NVSL/QuadClass-Remote/images/IMG_7027.jpg

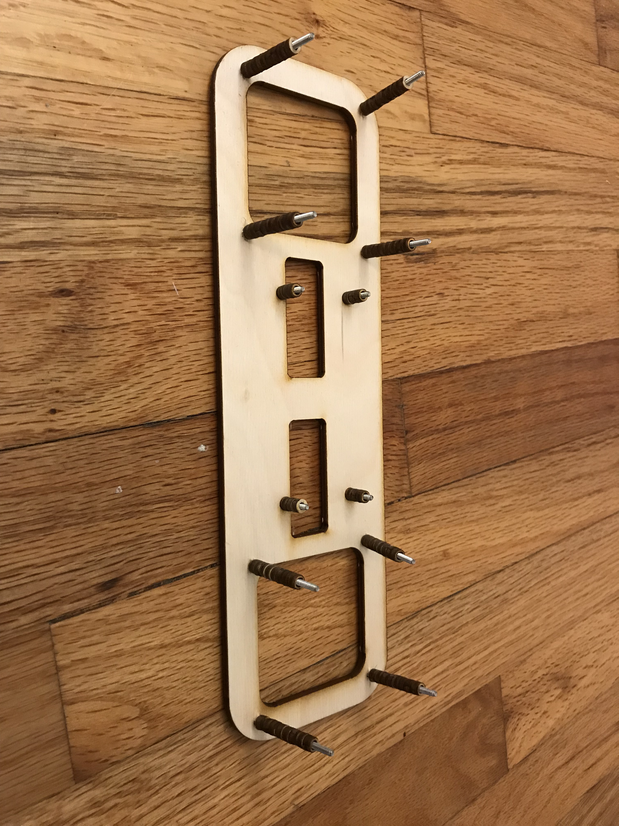
images/IMG_7027.jpg
