NVSL/QuadClass-Remote/images/IMG_7028.jpg

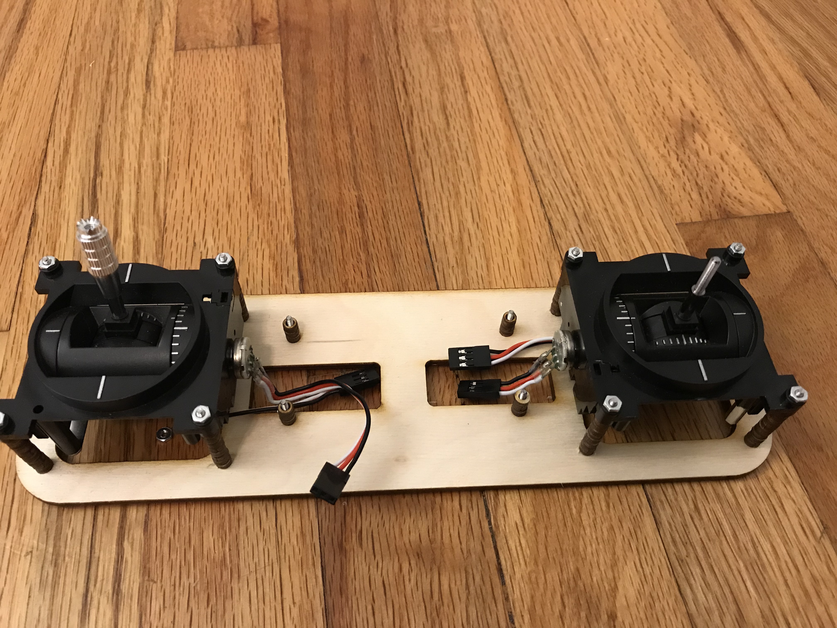
images/IMG_7028.jpg
