NVSL/QuadClass-Remote/images/IMG_7030.jpg

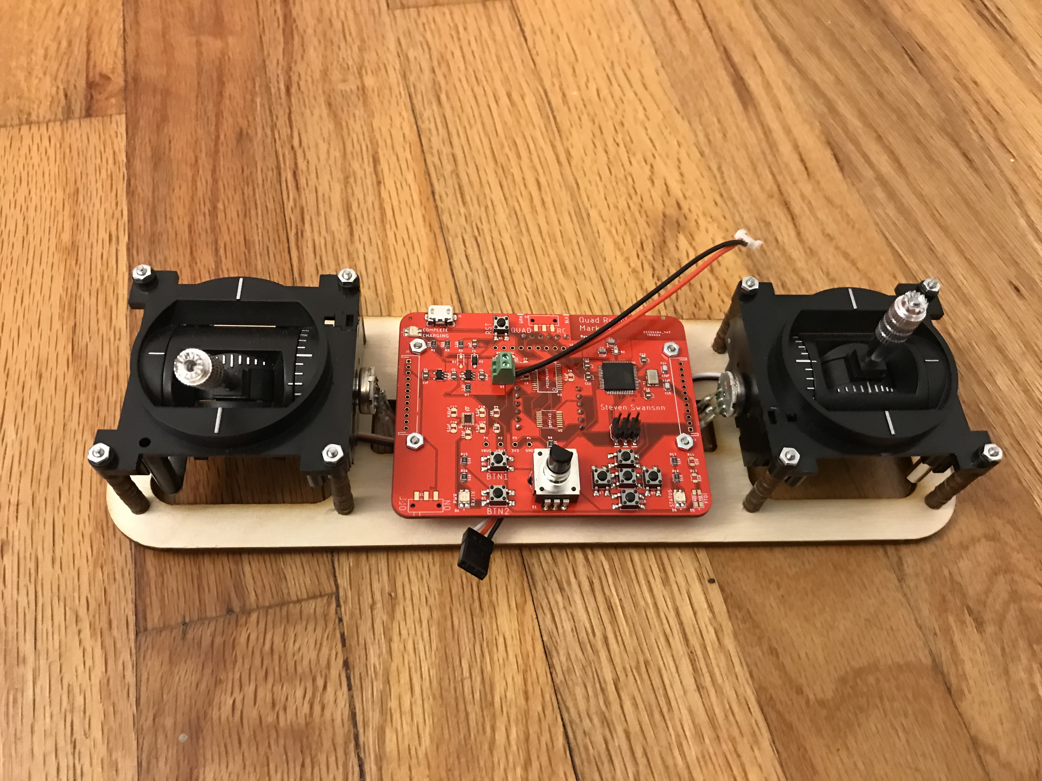
images/IMG_7030.jpg
