NVSL/QuadClass-Remote/images/IMG_7031.jpg

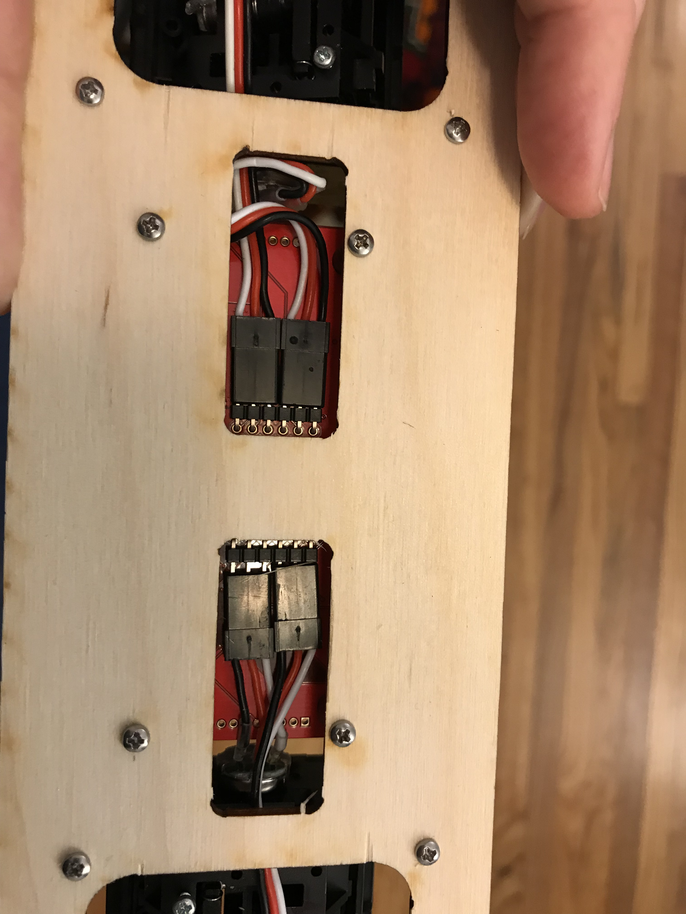
images/IMG_7031.jpg
