NVSL/QuadClass-Remote/images/IMG_7032.jpg

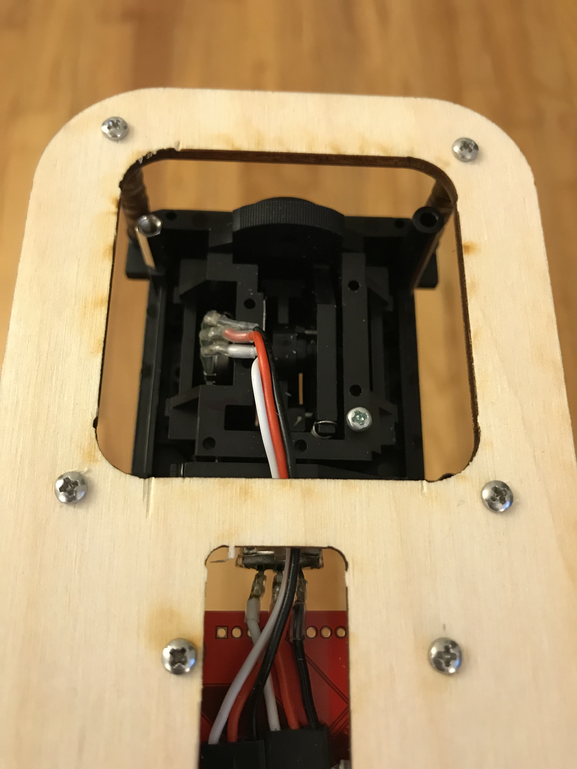
images/IMG_7032.jpg
