NVSL/QuadClass-Remote/multicharger/multicharger.brd

## EAGLE design multicharger/multicharger.brd (2020-02-13)

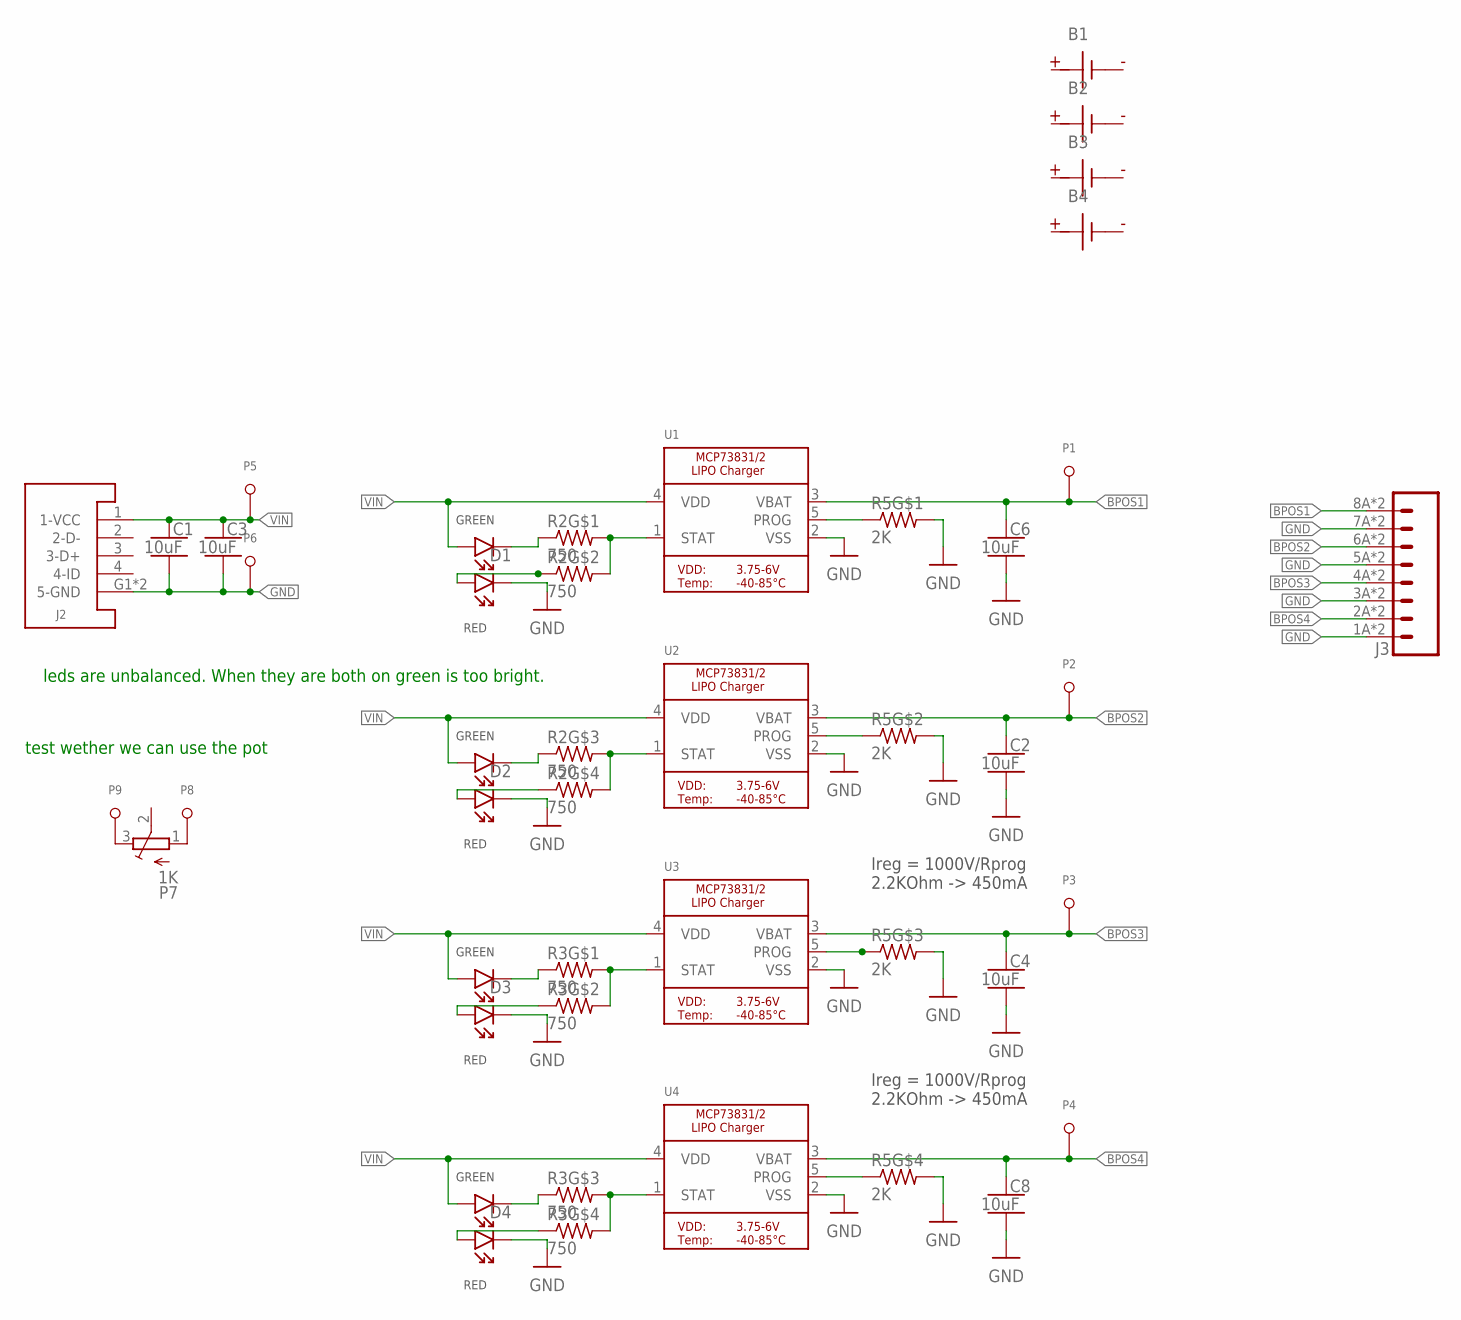
[picture p17: schematic multicharger.sch]

Parts:
B1, B2, B3, B4: BATTERY-SMD; MOLEX-BATTERY-CONNECTOR-SMD-51005-2P
C1, C2, C3, C4, C6, C8: 10uF; CAPC1608X100
D1, D2, D3, D4: LED-2X-GREEN/RED-1.6X1.5MM; LED-2X-LITE-ON-1.6MMX1.5MM
J2: USB-A-SMD-KEYSTONE-931; USB-A-KEYSTONE-931
J3: HEADER-8POS-; WIRE-TERMINAL-1X8-2.5MM-SMD
P1, P2, P3, P4, P5, P6, P8, P9: TEST-POINT-1MM; TEST-POINT-1MM-VIA
P7: 1K; BOT-ADJUST-POT-3314R-1-103E
R2, R3: 750; RESCAXS50P200X100X45-8
R5: 2K; RESCAXS50P200X100X45-8
U1, U2, U3, U4: MCP73831T-2ACI/OT; SOT23-5

Connections:
BPOS1: C6.1, J3.8A (8), J3.8B (8), P1.T, U1.3 (VBAT)
BPOS2: C2.1, J3.6A (6), J3.6B (6), P2.T, U2.3 (VBAT)
BPOS3: C4.1, J3.4A (4), J3.4B (4), P3.T, U3.3 (VBAT)
BPOS4: C8.1, J3.2A (2), J3.2B (2), P4.T, U4.3 (VBAT)
GND: C1.2, C2.2, C3.2, C4.2, C6.2, C8.2, D1.C1, D2.C1, D3.C1, D4.C1, J2.G1 (5-GND), J2.G2 (5-GND), J3.1A (1), J3.1B (1), J3.3A (3), J3.3B (3), J3.5A (5), J3.5B (5), J3.7A (7), J3.7B (7), P6.T, R5.5 (2), R5.6 (2), R5.7 (2), R5.8 (2), U1.2 (VSS), U2.2 (VSS), U3.2 (VSS), U4.2 (VSS)
unnamed: D1.A1, R2.3 (1)
unnamed: D1.C2, R2.4 (1)
unnamed: R2.7 (2), R2.8 (2), U2.1 (STAT)
unnamed: R5.3 (1), U2.5 (PROG)
unnamed: D2.A1, R2.1
unnamed: D2.C2, R2.2 (1)
unnamed: R3.5 (2), R3.6 (2), U3.1 (STAT)
unnamed: R5.2 (1), U3.5 (PROG)
unnamed: D3.A1, R3.3 (1)
unnamed: D3.C2, R3.4 (1)
unnamed: R2.5 (2), R2.6 (2), U1.1 (STAT)
unnamed: R5.4 (1), U1.5 (PROG)
unnamed: R3.7 (2), R3.8 (2), U4.1 (STAT)
unnamed: R5.1, U4.5 (PROG)
unnamed: D4.A1, R3.1
unnamed: D4.C2, R3.2 (1)
unnamed: P7.1 (A), P8.T
unnamed: P7.3 (E), P9.T
VIN: C1.1, C3.1, D1.A2, D2.A2, D3.A2, D4.A2, J2.1 (1-VCC), P5.T, U1.4 (VDD), U2.4 (VDD), U3.4 (VDD), U4.4 (VDD)

Notes on the sheet:
Ireg = 1000V/Rprog 2.2KOhm -> 450mA
leds are unbalanced. When they are both on green is too bright.
test wether we can use the pot

Board: 4 copper layers, 33 parts (7 on the bottom side), 24 nets, no tracks yet.

Other parts of the board:
U$2: QUADCLASS_LOGO
