NVSL/QuadClass-Remote/hardware/releases/v4-rev5-rc1/controller_board.brd

## EAGLE design hardware/releases/v4-rev5-rc1/controller_board.brd (2019-02-21, an earlier design)

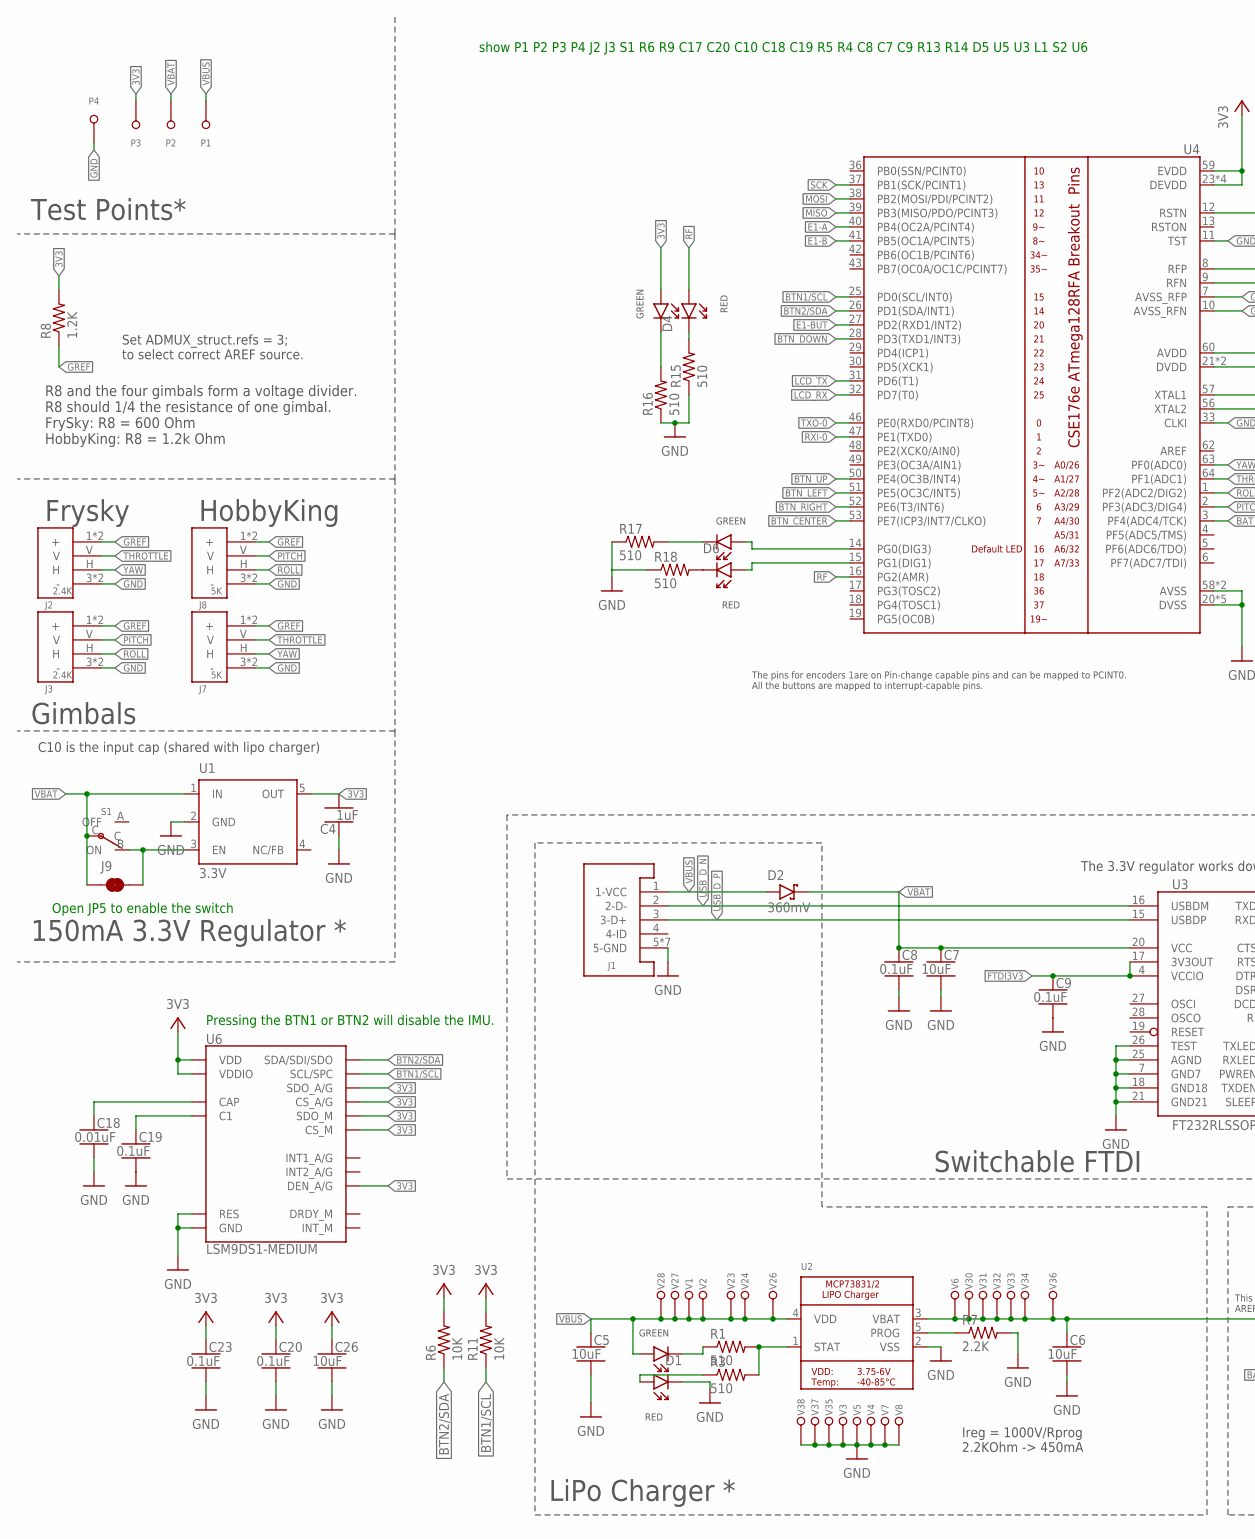
[picture p18: schematic controller_board.sch, part in row 1, column 1]

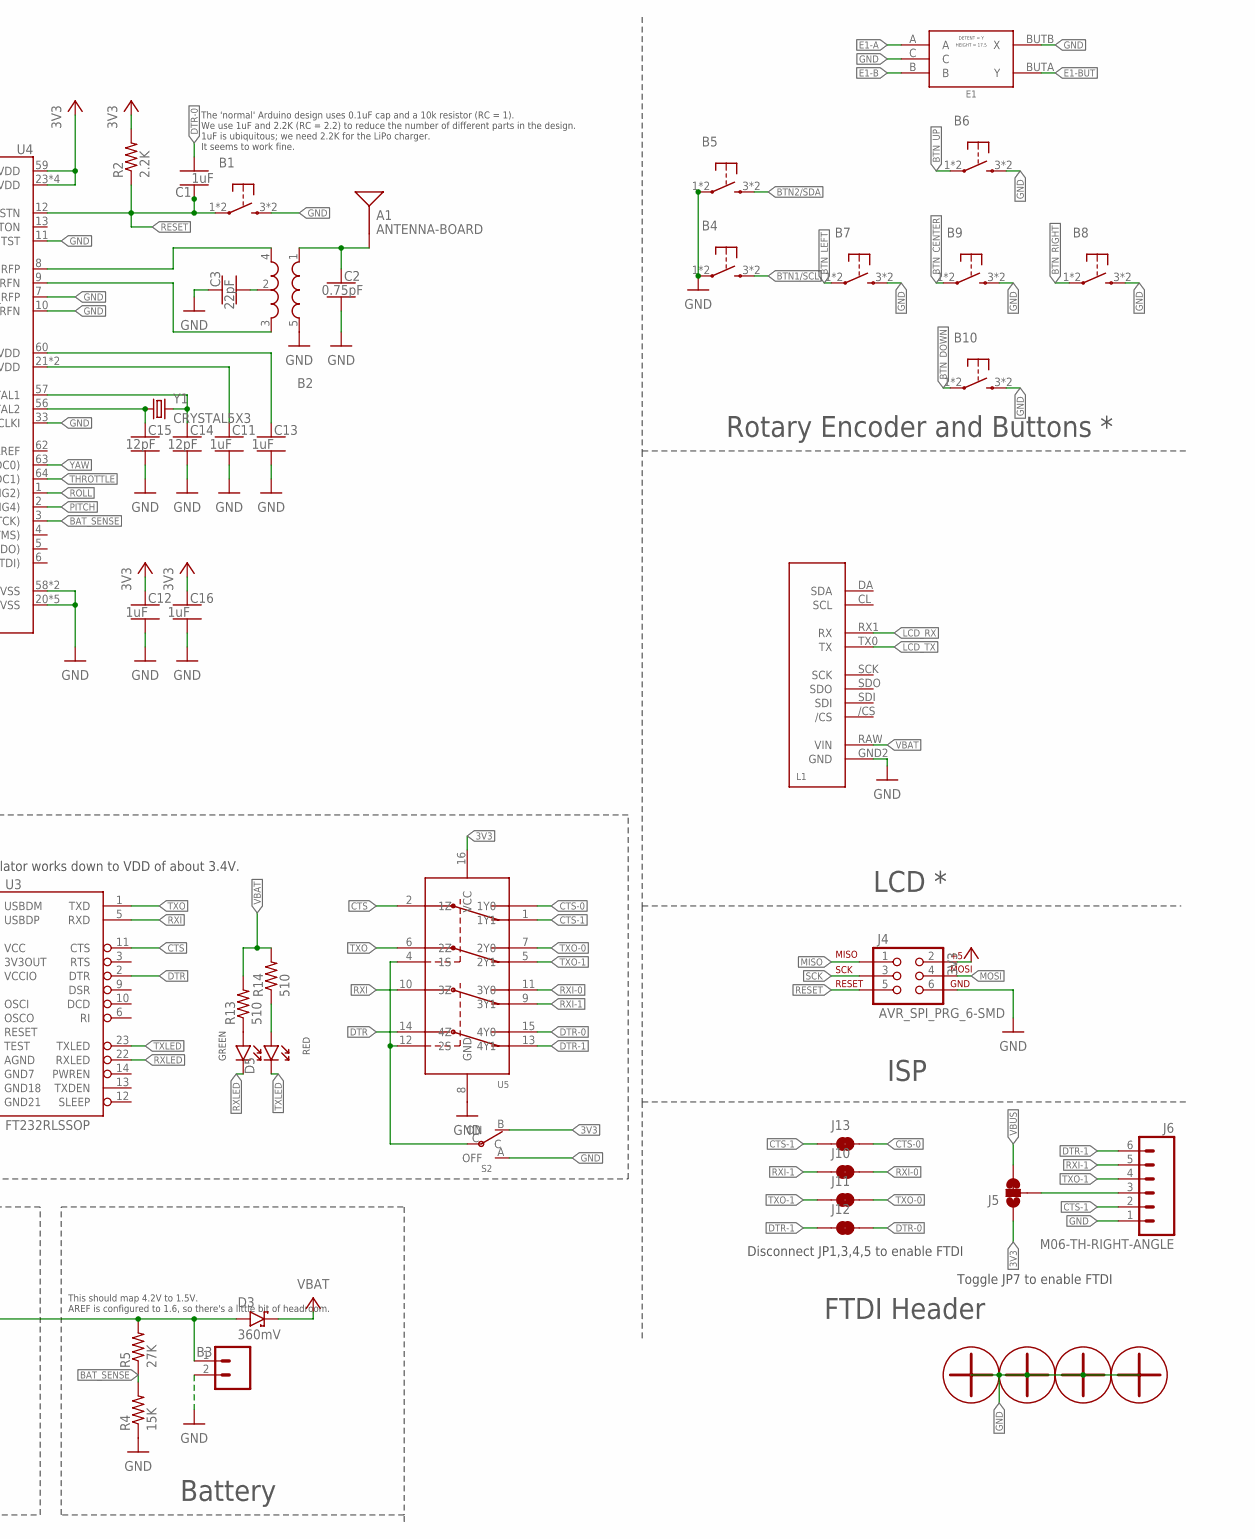
[picture p19: schematic controller_board.sch, part in row 1, column 2]

Parts:
A1: ANTENNA-BOARD; ANT_PCB_2.4GHZ_NRF8001_1.6MM_1OZ
B1, B4, B5, B6, B7, B8, B9, B10: PUSHBUTTON_-4.5X4.5; 4.5MM_TACTILE_SWITCH_TL3305AF160QG
B2: BALUN0805; BALUN
B3: HEADER-0.1IN-2POS-SCREW; SCREW-TERMINAL-1X2-2.54MM
C1, C4, C11, C12, C13, C16: 1uF; CAPC2012X140_HS
C2: 0.75pF; CAPC2012X140_HS
C3: 22pF; CAPC2012X140_HS
C5, C6, C7, C26: 10uF; CAPC2012X140_HS
C8, C9, C19, C20, C23: 0.1uF; CAPC2012X140_HS
C14, C15: 12pF; CAPC2012X140_HS
C18: 0.01uF; CAPC2012X140_HS
D1, D4, D5, D6: LED-2X-GREEN/RED; LED-2X-LTST-C155
D2, D3: 360mV; SOD3716X135_HS
E1: ROTARY-ENCODER-W/BUTTON-BOURNS-PEC12R-4217F; BOURNS-PEC12R
H1, H2, H3, H4: MOUNTING-HOLE-2-56-GROUNDED; 2-56-MOUNTING-HOLE
J1: USB-MICROA-AMPHENOL-10118192-0001LF; USB-MICROA-10118192-0001LF
J2, J3: 2.4K; JST-13-PTH
J4: AVR_SPI_PRG_6-SMD; 2X3-SMD
J5: JUMPER-SMT_3_1-NC_TRACE_NO-SILK; SMT-JUMPER_3_1-NC_TRACE_NO-SILK
J6: M06-TH-RIGHT-ANGLE; 1X06-SIP-RIGHT-ANGLE
J7, J8: 5K; 2X-GIMBAL-SERVO
J9, J10, J11, J12, J13: JUMPER-SMT_2_NC_TRACE_NO-SILK; SMT-JUMPER_2_NC_TRACE_NO-SILK
L1: SPARKFUN_SERLCD_SERIAL_REDUCED; SPARKFUN_SERLCD_16X2_REDUCED
P1, P2, P3, P4: TEST-POINT; TEST-POINT-KEYSTONE-5000
R1, R3, R13, R14, R15, R16, R17, R18: 510; RESC2012X60_HS
R2, R7: 2.2K; RESC2012X60_HS
R4: 15K; RESC2012X60_HS
R5: 27K; RESC2012X60_HS
R6, R11: 10K; RESC2012X60_HS
R8: 1.2K; RESC2012X60_HS
S1, S2: POWER-SWITCH-MFS201N-9-ZJS102011SAQN; JS102011SAQN
U1: 3.3V; SOT23-DBV
U2: MCP73831T-2ACI/OT; SOT23-5
U3: FT232RLSSOP; SSOP28DB
U4: ATMEGA128RFA1; QFN-64
U5: DPDT-X2; SOP65P640X110-16
U6: LSM9DS1-MEDIUM; NEW_IMU_MEDIUM
V1, V2, V3, V4, V5, V6, V7, V8, V23, V24, V26, V27, V28, V30, V31, V32, V33, V34, V35, V36, V37, V38: LOCKED-VIA-0.2; VIA-0.2MM
Y1: CRYSTAL5X3; CRYSTAL-SMD-5X3

Connections:
3V3: C4.2, C12.1, C16.1, C20.1, C23.1, C26.1, D4.A2, J4.2, J5.1, P3.T, R2.2, R6.2, R8.2, R11.2, S2.B (ON), U1.5 (OUT), U4.23 (DEVDD), U4.34 (DEVDD), U4.44 (DEVDD), U4.54 (DEVDD), U4.59 (EVDD), U5.16 (VCC), U6.CS_A/G, U6.CS_M, U6.DEN_A/G, U6.SDO_A/G, U6.SDO_M, U6.VDD1 (VDD), U6.VDD2 (VDD), U6.VDDIO, U6.VDDIO2 (VDDIO)
ANTENNA: A1.FEED, B2.1 (IN), C2.1
BAT_SENSE: R4.2, R5.1, U4.3 (PF4(ADC4/TCK))
BCAP: B2.2 (GND), C3.2
BPOS: B3.1, C6.1, D3.A, R5.2, U2.3 (VBAT), V6.P1, V30.P1, V31.P1, V32.P1, V33.P1, V34.P1, V36.P1
BTN1/SCL: B4.3 (2), B4.4 (2), R11.1, U4.25 (PD0(SCL/INT0)), U6.SCL/SPC
BTN2/SDA: B5.3 (2), B5.4 (2), R6.1, U4.26 (PD1(SDA/INT1)), U6.SDA/SDI/SDO
BTN_CENTER: B9.1, B9.2 (1), U4.53 (PE7(ICP3/INT7/CLKO))
BTN_DOWN: B10.1, B10.2 (1), U4.28 (PD3(TXD1/INT3))
BTN_LEFT: B7.1, B7.2 (1), U4.51 (PE5(OC3C/INT5))
BTN_RIGHT: B8.1, B8.2 (1), U4.52 (PE6(T3/INT6))
BTN_UP: B6.1, B6.2 (1), U4.50 (PE4(OC3B/INT4))
CLK_NEG: C15.1, U4.56 (XTAL2), Y1.1
CLK_POS: C14.1, U4.57 (XTAL1), Y1.3 (2)
CTS: U3.11 (CTS), U5.2 (1Z)
CTS-0: J13.2, U5.3 (1Y0)
CTS-1: J6.2, J13.1, U5.1 (1Y1)
DTR: U3.2 (DTR), U5.14 (4Z)
DTR-0: C1.2, J12.2, U5.15 (4Y0)
DTR-1: J6.6, J12.1, U5.13 (4Y1)
E1-A: E1.A, U4.40 (PB4(OC2A/PCINT4))
E1-B: E1.B, U4.41 (PB5(OC1A/PCINT5))
E1-BUT: E1.BUTA (Y), U4.27 (PD2(RXD1/INT2))
FTDI3V3: C9.1, U3.4 (VCCIO), U3.17 (3V3OUT)
FTDI_VDD: J5.2, J6.3
GND: B1.3 (2), B1.4 (2), B2.5 (GND), B3.2, B4.1, B4.2 (1), B5.1, B5.2 (1), B6.3 (2), B6.4 (2), B7.3 (2), B7.4 (2), B8.3 (2), B8.4 (2), B9.3 (2), B9.4 (2), B10.3 (2), B10.4 (2), C2.2, C3.1, C4.1, C5.2, C6.2, C7.2, C8.2, C9.2, C11.2, C12.2, C13.2, C14.2, C15.2, C16.2, C18.2, C19.2, C20.2, C23.2, C26.2, D1.C1, E1.BUTB (X), E1.C, H1.1, H1.2, H1.3, H1.4, H1.5, H1.6, H1.7, H1.8, H2.1, H2.2, H2.3, H2.4, H2.5, H2.6, H2.7, H2.8, H3.1, H3.2, H3.3, H3.4, H3.5, H3.6, H3.7, H3.8, H4.1, H4.2, H4.3, H4.4, H4.5, H4.6, H4.7, H4.8, J1.5 (5-GND), J1.6 (5-GND), J1.7 (5-GND), J1.8 (5-GND), J1.9 (5-GND), J1.10 (5-GND), J1.11 (5-GND), J2.3 (-), J2.6 (-), J3.3 (-), J3.6 (-), J4.6, J6.1, J7.3 (-), J7.6 (-), J8.3 (-), J8.6 (-), L1.GND2 (GND), P4.T, R4.1, R7.2, R15.1, R16.1, R17.1, R18.1, S2.A (OFF), U1.2 (GND), U2.2 (VSS), U3.7 (GND7), U3.18 (GND18), U3.21 (GND21), U3.25 (AGND), U3.26 (TEST), U4.7 (AVSS_RFP), U4.10 (AVSS_RFN), U4.11 (TST), U4.20 (DVSS), U4.24 (DVSS), U4.33 (CLKI), U4.35 (DVSS), U4.45 (DVSS), U4.55 (DVSS), U4.58 (AVSS), U4.61 (AVSS), U5.8 (GND), U6.GND1 (GND), U6.GND2 (GND), U6.RES1 (RES), U6.RES2 (RES), U6.RES3 (RES), U6.RES4 (RES), U6.RES5 (RES), V3.P1, V4.P1, V5.P1, V7.P1, V8.P1, V35.P1, V37.P1, V38.P1
GREF: J2.1 (+), J2.4 (+), J3.1 (+), J3.4 (+), J7.1 (+), J7.4 (+), J8.1 (+), J8.4 (+), R8.1
LCD_RX: L1.RX1 (RX), U4.32 (PD7(T0))
LCD_TX: L1.TX0 (TX), U4.31 (PD6(T1))
MISO: J4.1, U4.39 (PB3(MISO/PDO/PCINT3))
MOSI: J4.4, U4.38 (PB2(MOSI/PDI/PCINT2))
unnamed: D1.A1, R3.1
unnamed: D1.C2, R1.1
unnamed: D5.A1, R14.1
unnamed: D6.C2, R17.2
unnamed: C18.1, U6.CAP
unnamed: D4.C1, R15.2
unnamed: C19.1, U6.C1
unnamed: D6.A2, U4.14 (PG0(DIG3))
unnamed: D6.A1, U4.15 (PG1(DIG1))
unnamed: R1.2, R3.2, U2.1 (STAT)
unnamed: R7.1, U2.5 (PROG)
unnamed: D4.C2, R16.2
unnamed: D5.A2, R13.1
unnamed: J9.2, S1.B (ON), U1.3 (EN)
unnamed: C11.1, U4.21 (DVDD), U4.22 (DVDD)
unnamed: C13.1, U4.60 (AVDD)
unnamed: D6.C1, R18.2
PITCH: J3.V, J8.V, U4.2 (PF3(ADC3/DIG4))
PROG_SEL: S2.C, U5.4 (1S), U5.12 (2S)
RESET: B1.1, B1.2 (1), C1.1, J4.5, R2.1, U4.12 (RSTN)
RF: D4.A1, U4.16 (PG2(AMR))
RFN: B2.3 (OUT2), U4.9 (RFN)
RFP: B2.4 (OUT1), U4.8 (RFP)
ROLL: J3.H, J8.H, U4.1 (PF2(ADC2/DIG2))
RXI: U3.5 (RXD), U5.10 (3Z)
RXI-0: J10.2, U4.47 (PE1(TXD0)), U5.11 (3Y0)
RXI-1: J6.5, J10.1, U5.9 (3Y1)
RXLED: D5.C2, U3.22 (RXLED)
SCK: J4.3, U4.37 (PB1(SCK/PCINT1))
THROTTLE: J2.V, J7.V, U4.64 (PF1(ADC1))
TXLED: D5.C1, U3.23 (TXLED)
TXO: U3.1 (TXD), U5.6 (2Z)
TXO-0: J11.2, U4.46 (PE0(RXD0/PCINT8)), U5.7 (2Y0)
TXO-1: J6.4, J11.1, U5.5 (2Y1)
USB_D_N: J1.2 (2-D-), U3.16 (USBDM)
USB_D_P: J1.3 (3-D+), U3.15 (USBDP)
VBAT: C7.1, C8.1, D2.C, D3.C, J9.1, L1.RAW (VIN), P2.T, R13.2, R14.2, S1.C, U1.1 (IN), U3.20 (VCC)
VBUS: C5.1, D1.A2, D2.A, J1.1 (1-VCC), J5.3, P1.T, U2.4 (VDD), V1.P1, V2.P1, V23.P1, V24.P1, V26.P1, V27.P1, V28.P1
YAW: J2.H, J7.H, U4.63 (PF0(ADC0))

Notes on the sheet:
Ireg = 1000V/Rprog 2.2KOhm -> 450mA
The 3.3V regulator works down to VDD of about 3.4V.
This should map 4.2V to 1.5V. AREF is configured to 1.6, so there's a little bit of headroom.
The pins for encoders 1are on Pin-change capable pins and can be mapped to PCINT0. All the buttons are mapped to interrupt-capable pins.
LiPo Charger *
Switchable FTDI
Test Points*
Frysky
HobbyKing
Rotary Encoder and Buttons *
Battery
LCD *
ISP
FTDI Header
150mA 3.3V Regulator *
show P1 P2 P3 P4 J2 J3 S1 R6 R9 C17 C20 C10 C18 C19 R5 R4 C8 C7 C9 R13 R14 D5 U5 U3 L1 S2 U6
C10 is the input cap (shared with lipo charger)
The 'normal' Arduino design uses 0.1uF cap and a 10k resistor (RC = 1). We use 1uF and 2.2K (RC = 2.2) to reduce the number of different parts in the design. 1uF is ubiquitous; we need 2.2K for the LiPo charger. It seems to work fine.
Toggle JP7 to enable FTDI
Disconnect JP1,3,4,5 to enable FTDI
Set ADMUX_struct.refs = 3; to select correct AREF source.
Open JP5 to enable the switch
Gimbals
R8 and the four gimbals form a voltage divider. R8 should 1/4 the resistance of one gimbal. FrySky: R8 = 600 Ohm HobbyKing: R8 = 1.2k Ohm
Pressing the BTN1 or BTN2 will disable the IMU.

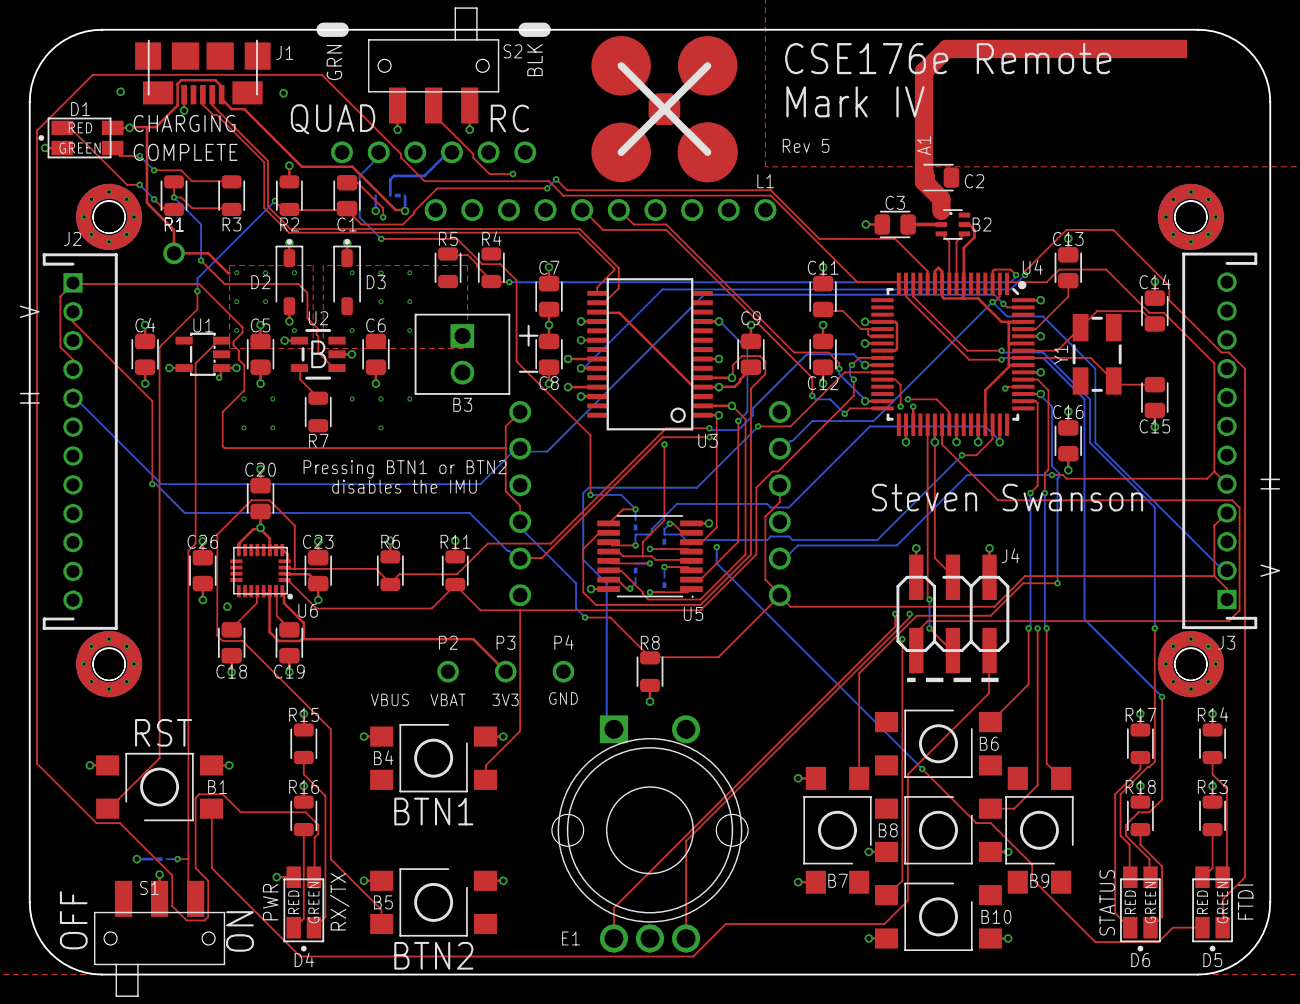
[picture p20: board hardware/releases/v4-rev5-rc1/controller_board.brd from above]

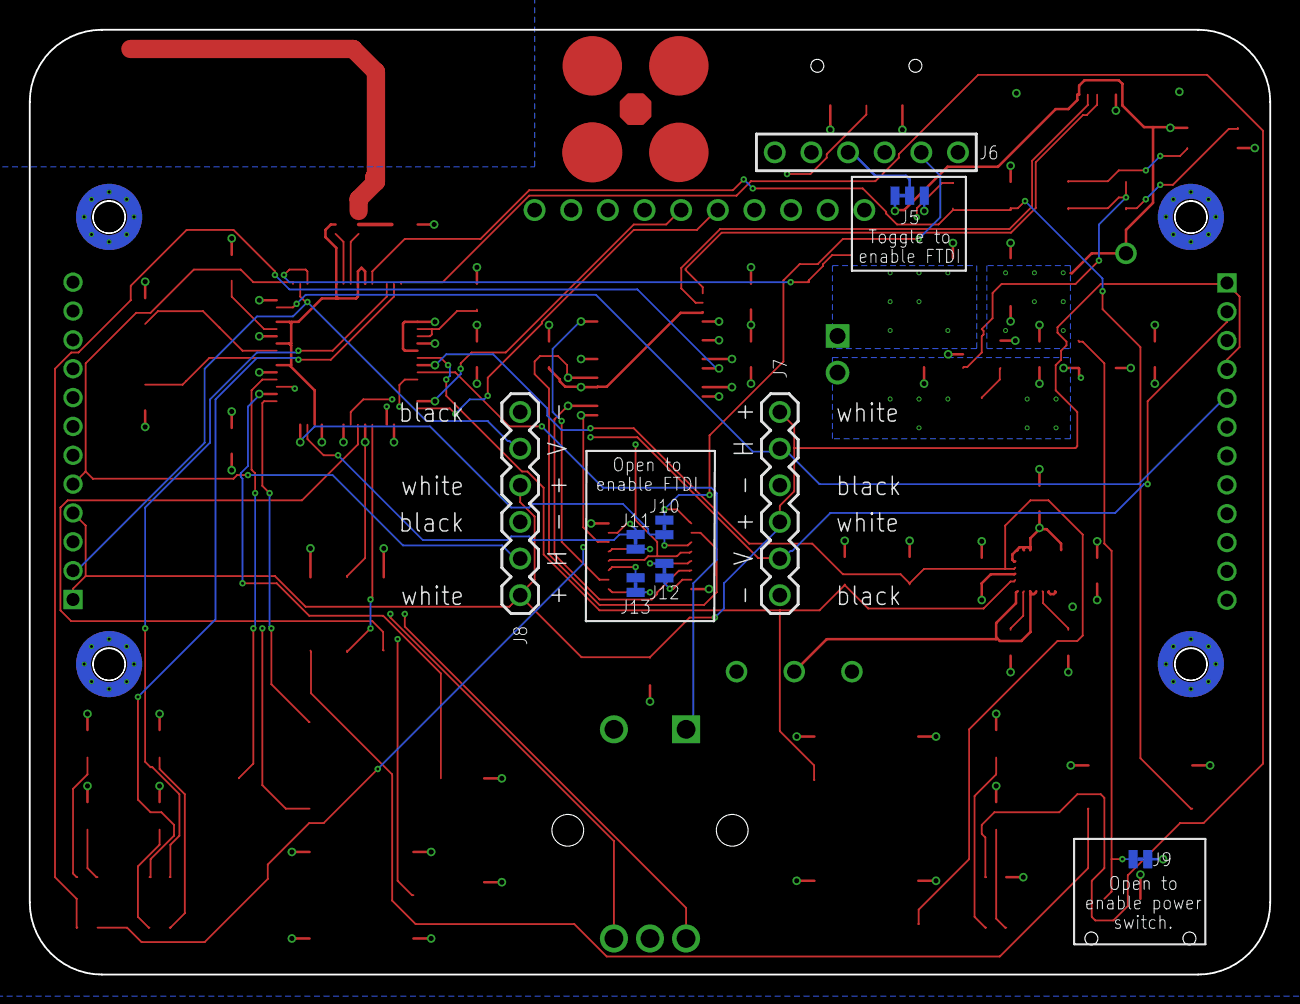
[picture p21: board hardware/releases/v4-rev5-rc1/controller_board.brd from below]

Board: 4 copper layers, 86.0 x 65.5 mm, 234 parts (9 on the bottom side), 70 nets.

Other parts of the board:
E$1, E$2: FRSKY-TARANIS-GIMBAL
U$1: LAYER_LABELS
U$4: 375MAH-BATTERY
U$5: 600MAH-BATTERY
U$8, U$10, U$14, U$15, U$16, U$17, U$18, U$19, U$20, U$21, U$22, U$23, U$24, U$25, U$26, U$27, U$28, U$29, U$30, U$31, U$32, U$33, U$34, U$35, U$36, U$37, U$38, U$39, U$40, U$41, U$42, U$43, U$44, U$45, U$46, U$47, U$48, U$49, U$50, U$51, U$52, U$53, U$54, U$55, U$56, U$57, U$58, U$59, U$60, U$61, U$62, U$63, U$64, U$65, U$66, U$67, U$68, U$69, U$70, U$71, U$72, U$73, U$74, U$75, U$76, U$77, U$78, U$79, U$80, U$81, U$82, U$83, U$84, U$85, U$86, U$87, U$88, U$89, U$90, U$91, U$92, U$93, U$94, U$95, U$96, U$97, U$98, U$99, U$100, U$101, U$102, U$103, U$104, U$105, U$106, U$107, U$108, U$109, U$110, U$111, U$112, U$113, U$114, U$115, U$116, U$117, U$118, U$119, U$120, U$121, U$122, U$123, U$124, U$125, U$126, U$127, U$128, U$129, U$130, U$131, U$132, U$133: SUPPORT_DONUT
U$134: QUADCLASS_LOGO
