NVSL/QuadClass-Remote/hardware/power_test.brd

## EAGLE design hardware/power_test.brd (2018-06-05)

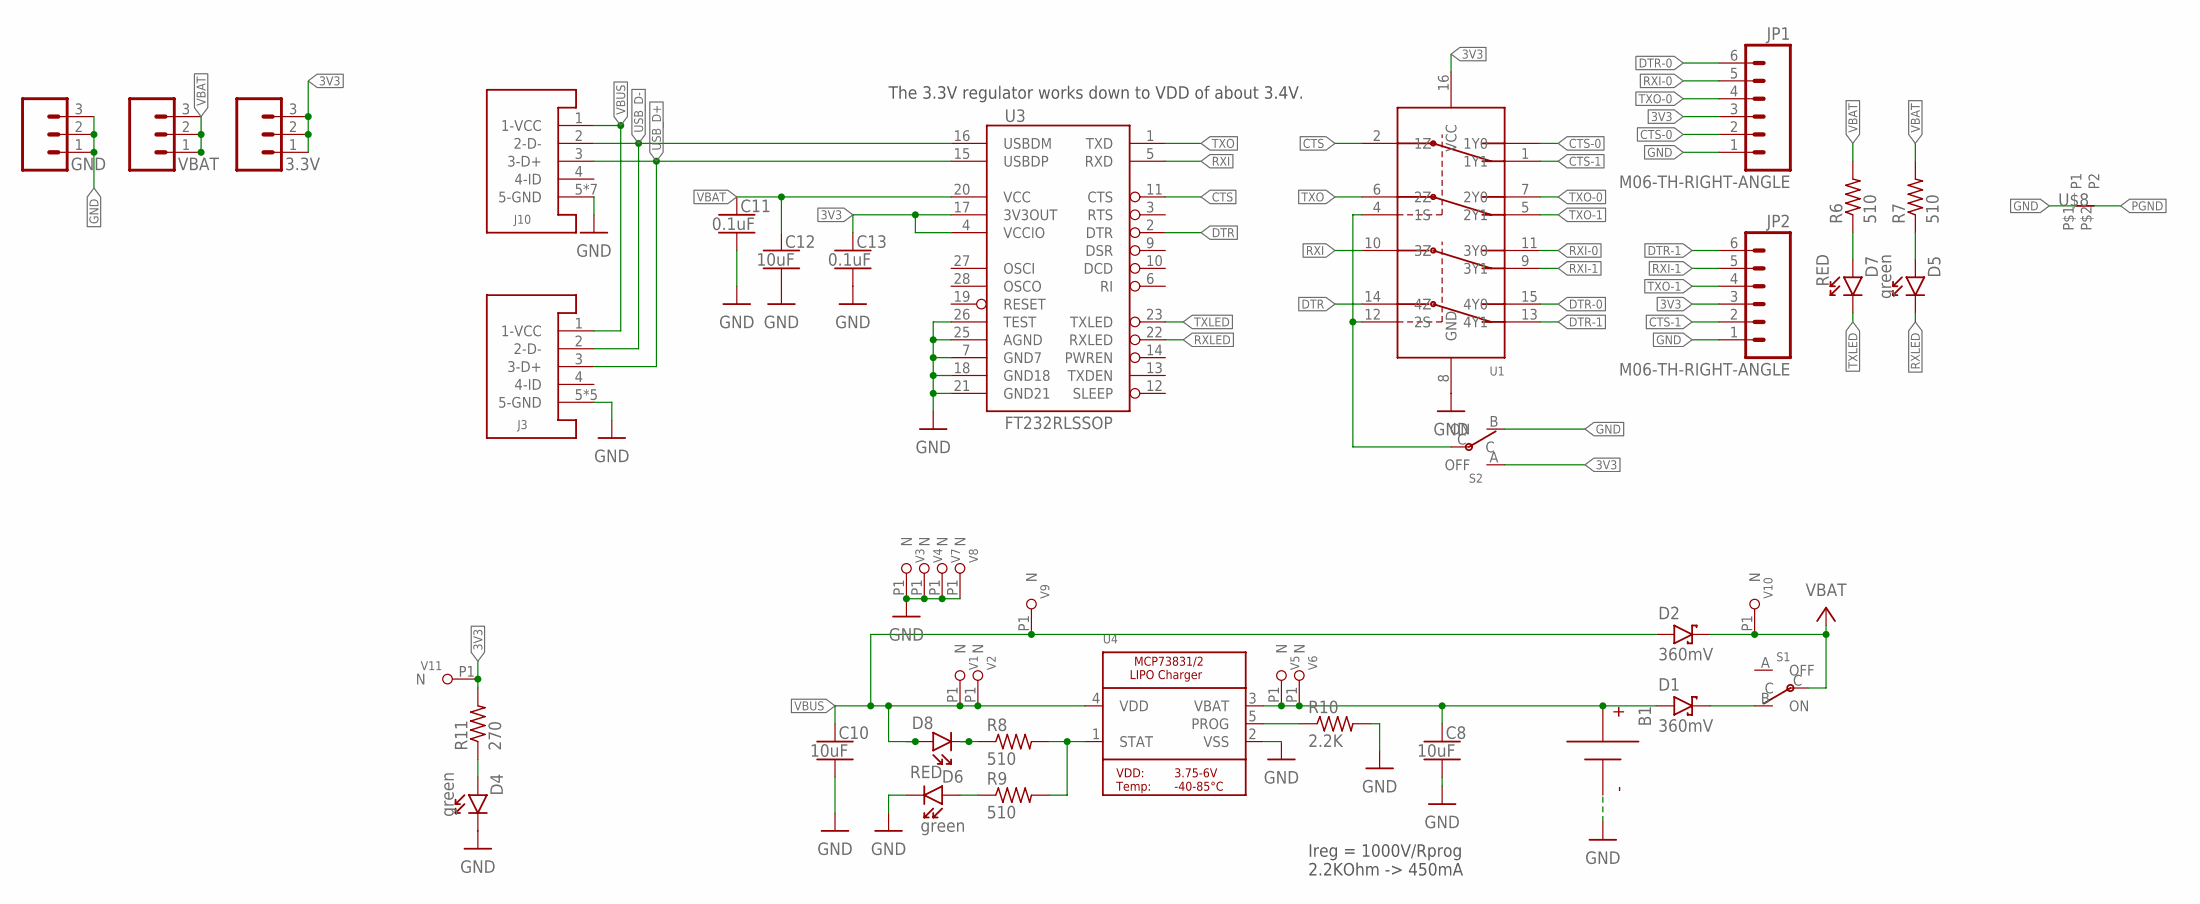
[picture p22: schematic power_test.sch]

Parts:
3.3V: HEADER-0.1IN-3POS-MALE; HDRV3W63P254_3X1_762X254H838_HS
B1: BATTERY; BATTERY-TERMINALS
C8, C10, C12: 10uF; CAPC2012X140_HS
C11, C13: 0.1uF; CAPC2012X140_HS
D1, D2: 360mV; SOD3716X135_HS
D4, D5, D6: green; LEDSC125X200X120-2_HS
D7, D8: RED; LEDSC125X200X120-2_HS
GND: HEADER-0.1IN-3POS-MALE; HDRV3W63P254_3X1_762X254H838_HS
J3: USB-MICROB-EDAC-690-005-299-043; USB-MINIB-EDAC-690-005-299-043
J10: USB-MICROA-AMPHENOL-10118192-0001LF; USB-MICROA-10118192-0001LF
JP1, JP2: M06-TH-RIGHT-ANGLE; 1X06-SIP-RIGHT-ANGLE
R6, R7, R8, R9: 510; RESC2012X60_HS
R10: 2.2K; RESC2012X60_HS
R11: 270; RESC2012X60_HS
S1, S2: POWER-SWITCH-MFS201N-9-ZJS102011SAQN; JS102011SAQN
U1: DPDT-X2; SOP65P640X110-16
U3: FT232RLSSOP; SSOP28DB
U4: MCP73831T-2ACI/OT; SOT23-5
U$8: NET_BRIDGE
V1, V2, V3, V4, V5, V6, V7, V8, V9, V10, V11: LOCKED-VIA-0.2; VIA-0.2MM
VBAT: HEADER-0.1IN-3POS-MALE; HDRV3W63P254_3X1_762X254H838_HS

Connections:
3V3: 3.3V.1, 3.3V.2, 3.3V.3, C13.1, JP1.3, JP2.3, R11.2, S2.A (OFF), U1.16 (VCC), U3.4 (VCCIO), U3.17 (3V3OUT), V11.P1
BPOS: B1.+, C8.1, D1.A, U4.3 (VBAT), V5.P1, V6.P1
CTS: U1.2 (1Z), U3.11 (CTS)
CTS-0: JP1.2, U1.3 (1Y0)
CTS-1: JP2.2, U1.1 (1Y1)
DTR: U1.14 (4Z), U3.2 (DTR)
DTR-0: JP1.6, U1.15 (4Y0)
DTR-1: JP2.6, U1.13 (4Y1)
GND: B1.- (N), C8.2, C10.2, C11.2, C12.2, C13.2, D4.C, D6.C, GND.1, GND.2, GND.3, J3.5 (5-GND), J3.P6 (5-GND), J3.P7 (5-GND), J3.P8 (5-GND), J3.P9 (5-GND), J10.5 (5-GND), J10.6 (5-GND), J10.7 (5-GND), J10.8 (5-GND), J10.9 (5-GND), J10.10 (5-GND), J10.11 (5-GND), JP1.1, JP2.1, R10.2, S2.B (ON), U1.8 (GND), U3.7 (GND7), U3.18 (GND18), U3.21 (GND21), U3.25 (AGND), U3.26 (TEST), U4.2 (VSS), U$8.P$1 (P1), V3.P1, V4.P1, V7.P1, V8.P1
unnamed: D7.A, R6.1
unnamed: D5.A, R7.1
unnamed: D8.C, R8.1
unnamed: R8.2, R9.2, U4.1 (STAT)
unnamed: R10.1, U4.5 (PROG)
unnamed: D6.A, R9.1
unnamed: D4.A, R11.1
unnamed: D1.C, S1.B (ON)
PGND: U$8.P$2 (P2)
PROG_SEL: S2.C, U1.4 (1S), U1.12 (2S)
RXI: U1.10 (3Z), U3.5 (RXD)
RXI-0: JP1.5, U1.11 (3Y0)
RXI-1: JP2.5, U1.9 (3Y1)
RXLED: D5.C, U3.22 (RXLED)
TXLED: D7.C, U3.23 (TXLED)
TXO: U1.6 (2Z), U3.1 (TXD)
TXO-0: JP1.4, U1.7 (2Y0)
TXO-1: JP2.4, U1.5 (2Y1)
USB_D+: J3.3 (3-D+), J10.3 (3-D+), U3.15 (USBDP)
USB_D-: J3.2 (2-D-), J10.2 (2-D-), U3.16 (USBDM)
VBAT: C11.1, C12.1, D2.C, R6.2, R7.2, S1.C, U3.20 (VCC), V10.P1, VBAT.1, VBAT.2, VBAT.3
VBUS: C10.1, D2.A, D8.A, J3.1 (1-VCC), J10.1 (1-VCC), U4.4 (VDD), V1.P1, V2.P1, V9.P1

Notes on the sheet:
Ireg = 1000V/Rprog 2.2KOhm -> 450mA
The 3.3V regulator works down to VDD of about 3.4V.

Board: 4 copper layers, 43 parts (1 on the bottom side), 30 nets, no tracks yet.
